umd-lhcb/electronic-projects/backplane/mechanics/19-02-08_stackup_mech_constraints_cern/stackup_28_layers/Stackup_report_for_PathFinder_24_layers.pdf

# STACKUP & IMPEDANCE REPORT

Page 1 of 1

### Planner: SSDC_AMITHR Confidential / Proprietary Information

### Customer Required Finished Thickness: 112.00 (+11.20 / -11.20) mils

### Measured: Over mask on plated copper

### Job Name: Customer:

152496

### Part Name:

### university of maryland Pathfinder

Revision: | A | Estimated Thickness after Lamination: 105.34 mils

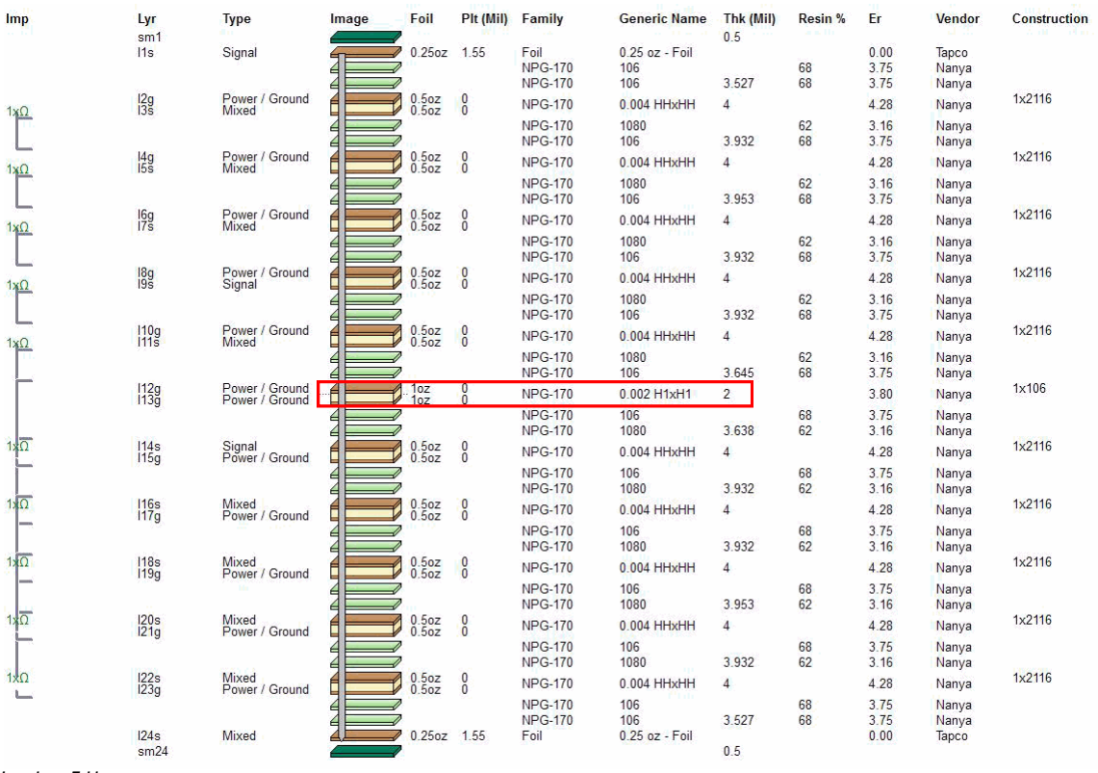
[picture p3: figure]

Index | Layer | Required Impedance [ohms] | Tol [ohms] +/- | Type | Ref 1 | Lower Ref | Orig LW [mil] | Orig Spacing [mil] | Orig CP Spacing [mil] | Finished LW [mil] | Finished Spacing [mil] | Fin. CP Spacing [mil] | Impedance Simulation [ohms] | Impedance before Mask [ohms] | IMG
a | 3 | 100 | 10% | Diff Stripline | 4 | 2 | 3.50 | 4.37 | | 3.00 | 4.87 | | 99.0
b | 5 | 100 | 10% | Diff Stripline | 6 | 4 | 3.50 | 4.37 | | 3.00 | 4.87 | | 99.1
c | 7 | 100 | 10% | Diff Stripline | 8 | 6 | 3.50 | 4.37 | | 3.00 | 4.87 | | 99.0
d | 9 | 100 | 10% | Diff Stripline | 10 | 8 | 3.50 | 4.37 | | 3.00 | 4.87 | | 99.0
e | 11 | 100 | 10% | Diff Stripline | 12 | 10 | 3.50 | 4.37 | | 3.00 | 4.87 | | 97.7
f | 14 | 100 | 10% | Diff Stripline | 13 | 15 | 3.50 | 4.37 | | 3.00 | 4.87 | | 97.7
g | 16 | 100 | 10% | Diff Stripline | 15 | 17 | 3.50 | 4.37 | | 3.00 | 4.87 | | 99.0
h | 18 | 100 | 10% | Diff Stripline | 17 | 19 | 3.50 | 4.37 | | 3.00 | 4.87 | | 99.0
i | 20 | 100 | 10% | Diff Stripline | 19 | 21 | 3.50 | 4.37 | | 3.00 | 4.87 | | 99.1
j | 22 | 100 | 10% | Diff Stripline | 21 | 23 | 3.50 | 4.37 | | 3.00 | 4.87 | | 99.0

Impedance Table

Report Version 1.60 | Report Print Date/Time: 11/16/2018 11:04:43AM | Page 1 of 1
