umd-lhcb/electronic-projects/lvr/UT_LV_DIAGRAMS.pdf

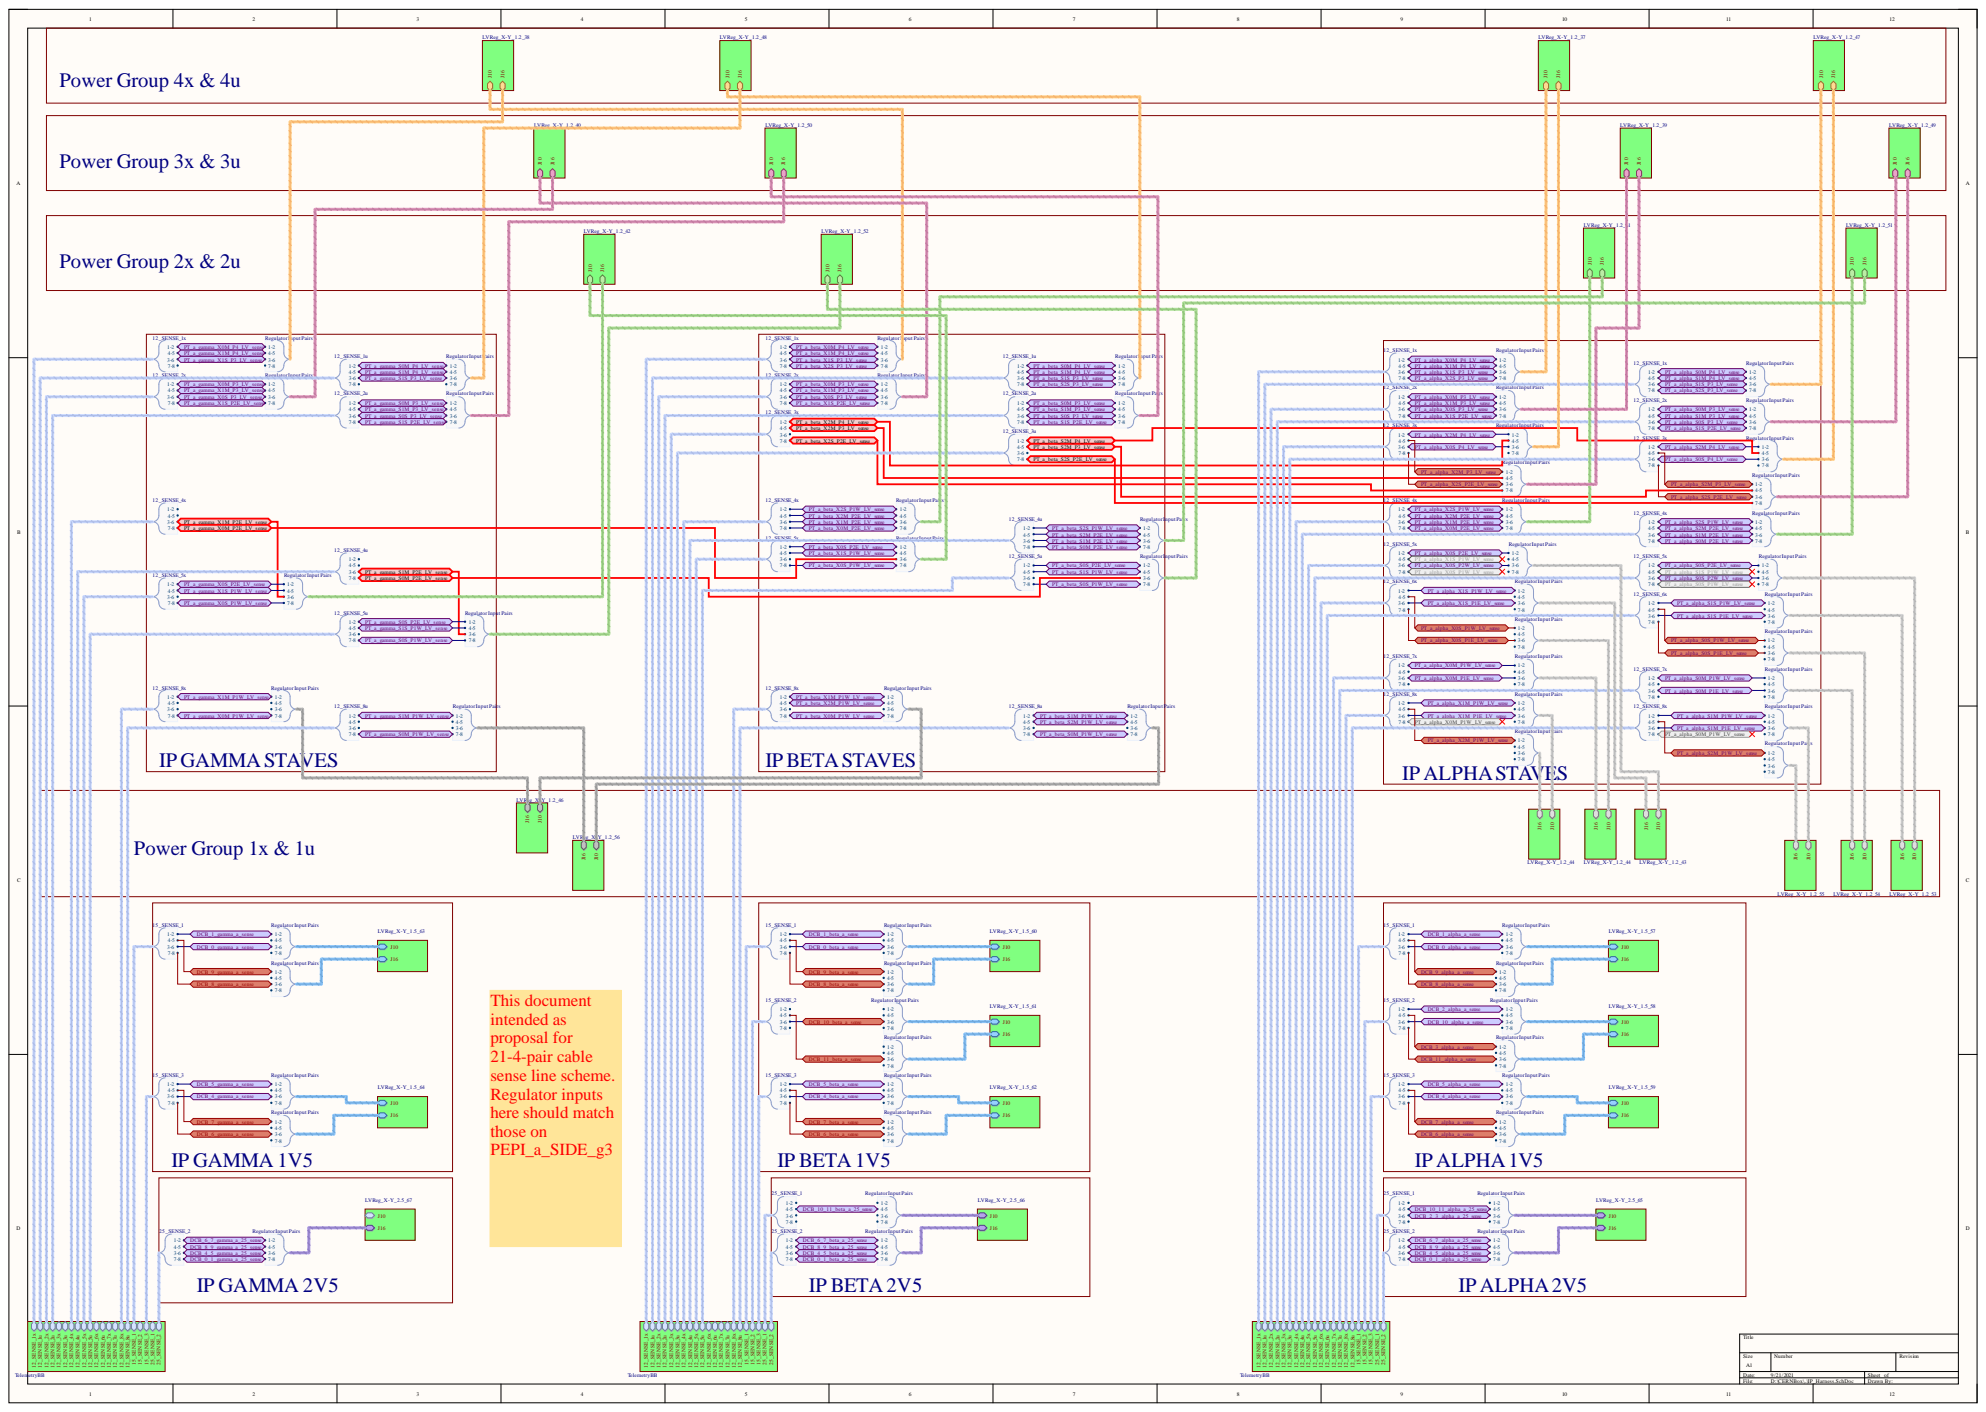
[picture p26: page 1]

12_SENSE_3u | | 1-2 PT_a_alpha_X2M_P4_LV_sense

4-5 PT_a_beta_S2M_P3_LV_sense 3-6 | | 3-6 7-8 | PT_a_alpha_X0S_P4_LV_sense | 1-2 PT_a_alpha_S2M_P4_LV_sense

PT_a_alpha_X2M_P3_LV_sense | Regulator Input Pairs 7-8 1-2 4-5 3-6 7-8 | PT_a_alpha_S2M_P3_LV_sense | 1-2 4-5 3-6 7-8

PT_a_alpha_X2S_P2E_LV_sense

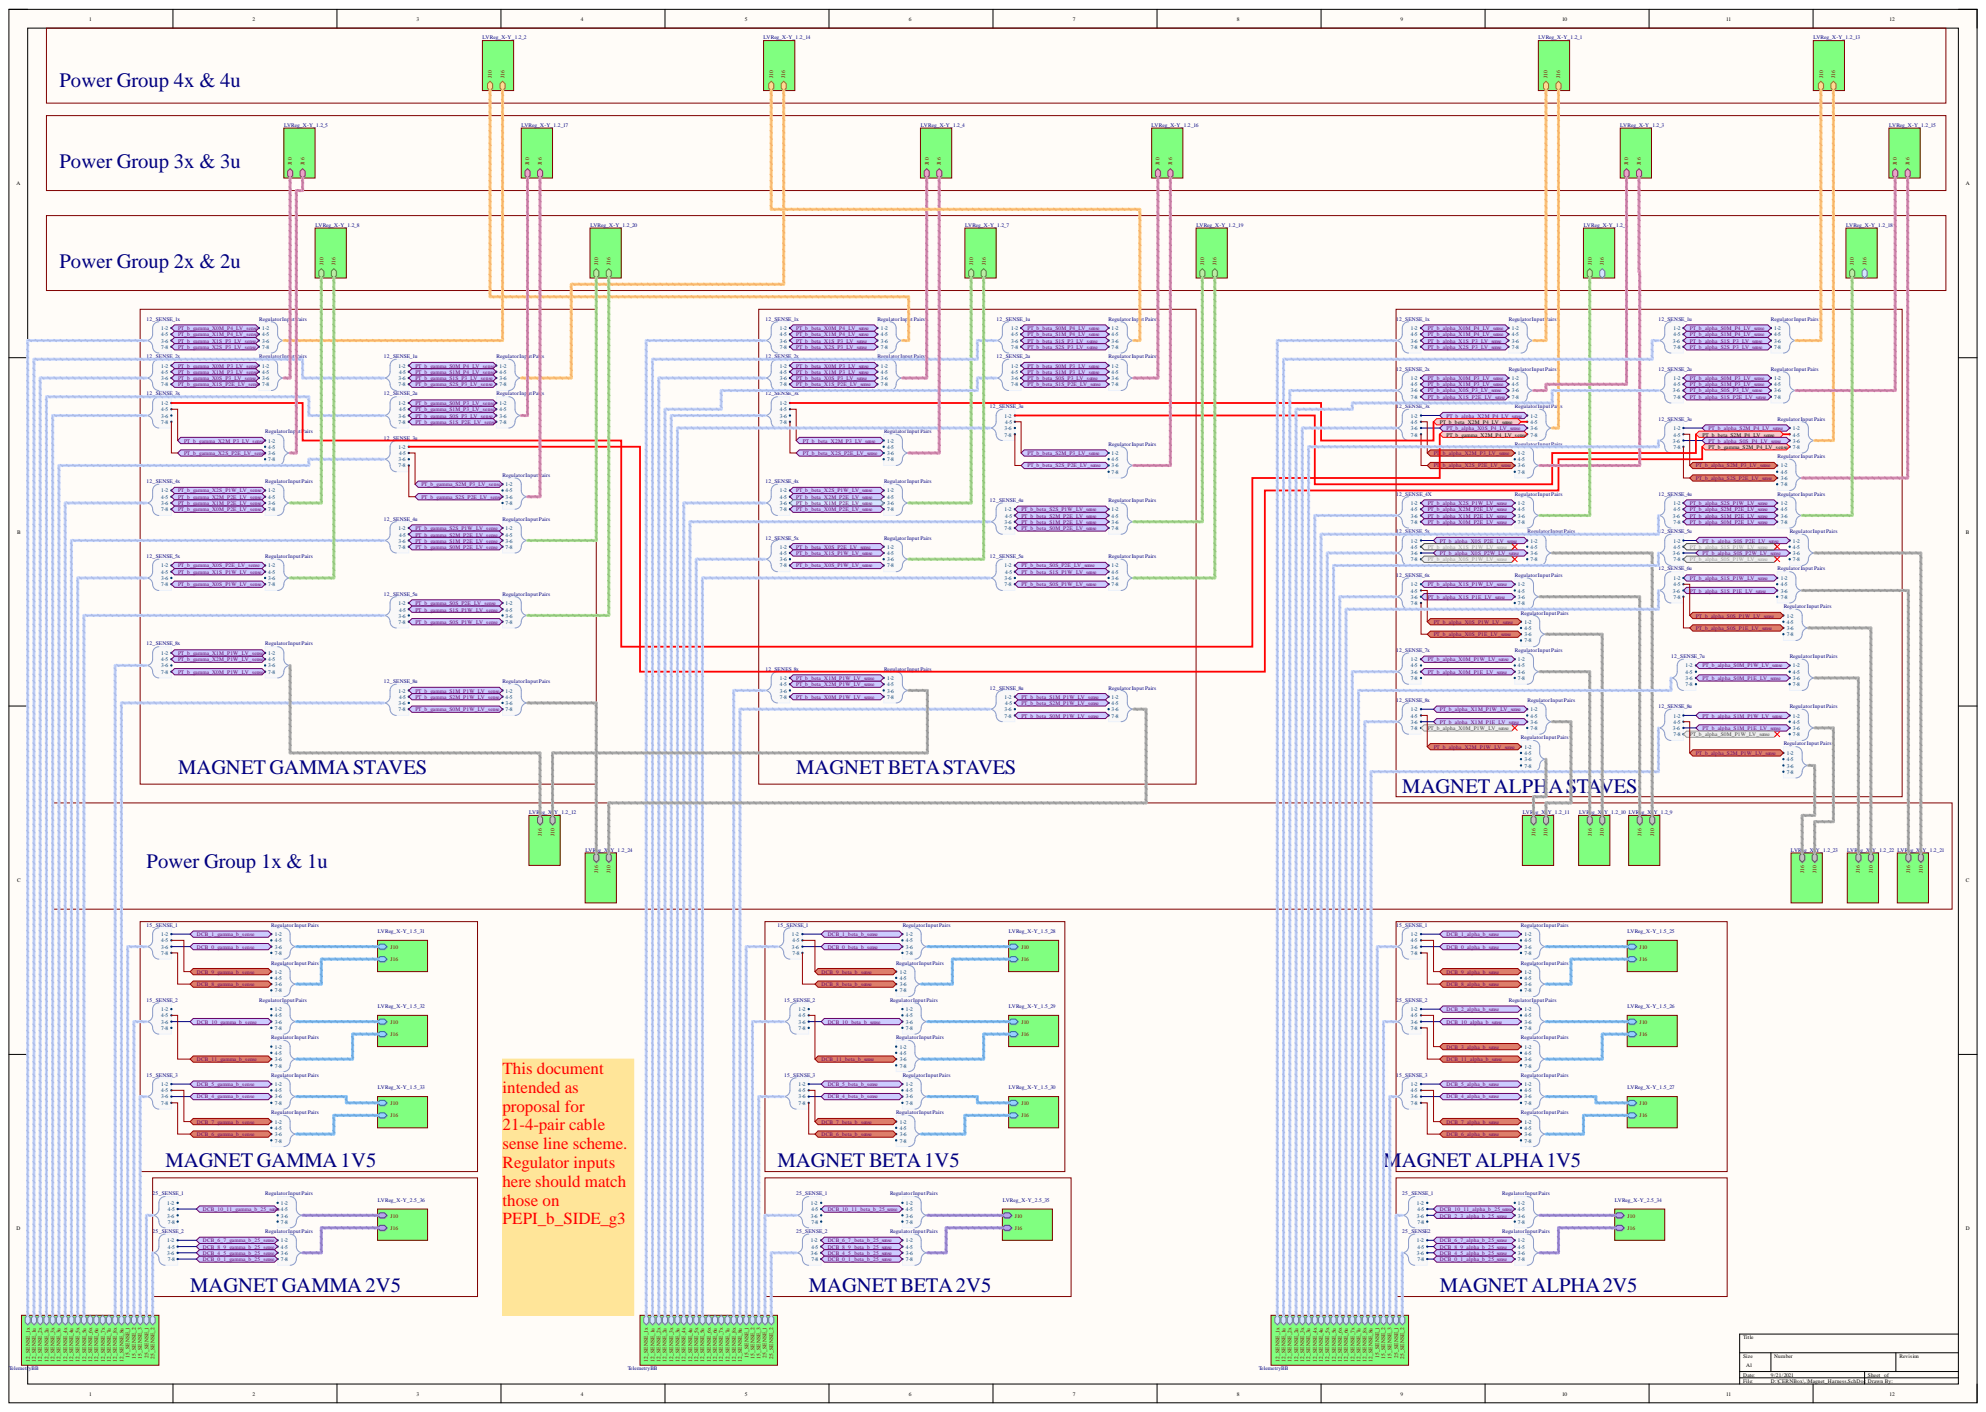
[picture p27: page 2]

7-8 PT_b_gamma_X1S_P2E_LV_sense 7-8 12_SENSE_3x

Regulator Input Pairs | 12_SENSE_3u 1-2 | 12_SENSE_3x 1-2

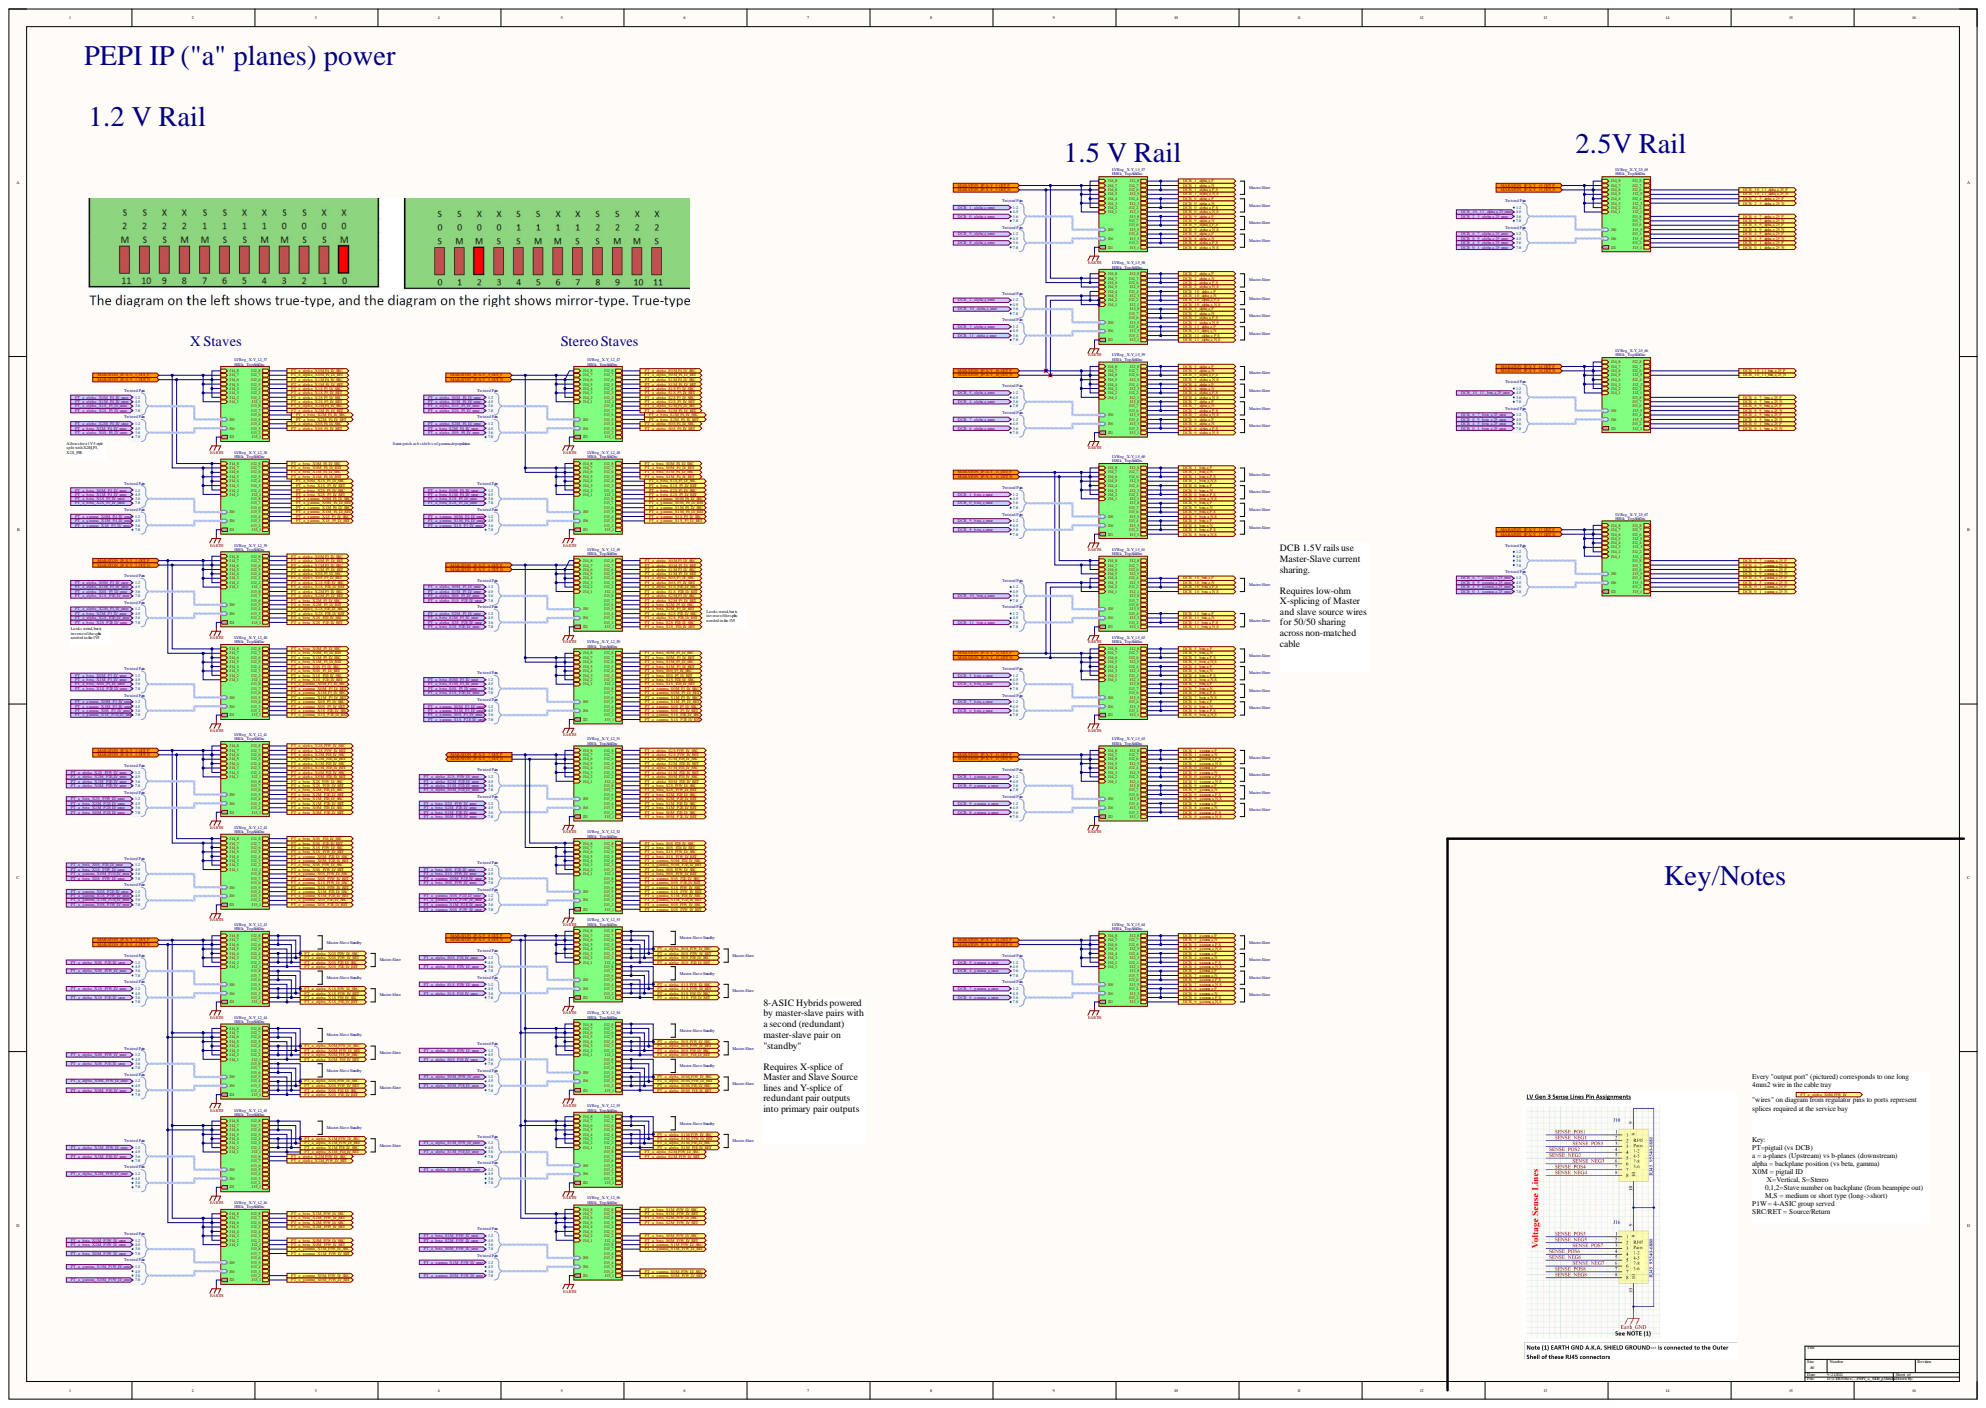
[picture p28: page 3]

PEPI IP ("a" planes) power

Same patch as b side b/c ofgamma depopulation

Requires low-ohm
X-splicing of Master
and slave source wires
for 50/50 sharing
across non-matched
cable

Looks weird, but is
inverse ofthe splits

8-ASIC Hybrids powered
by master-slave pairs with
a second (redundant)
master-slave pair on
"standby"

Requires X-splice of
Master and Slave Source
lines and Y-splice of
redundant pair outputs
into primary pair outputs

Every "output port" (pictured) corresponds to one long
4mm2 wire in the cable tray

"wires" on diagram from regulator pins to ports represent
splices required at the service bay

Key:
PT=pigtail (vs DCB)
a = a-planes (Upstream) vs b-planes (downstream)
alpha = backplane position (vs beta, gamma)
X0M = pigtail ID
X=Vertical, S=Stereo
0,1,2=Stave number on backplane (from beampipe out)
M,S = medium or short type (long->short)
P1W= 4-ASIC group served

SRC/RET = Source/Return

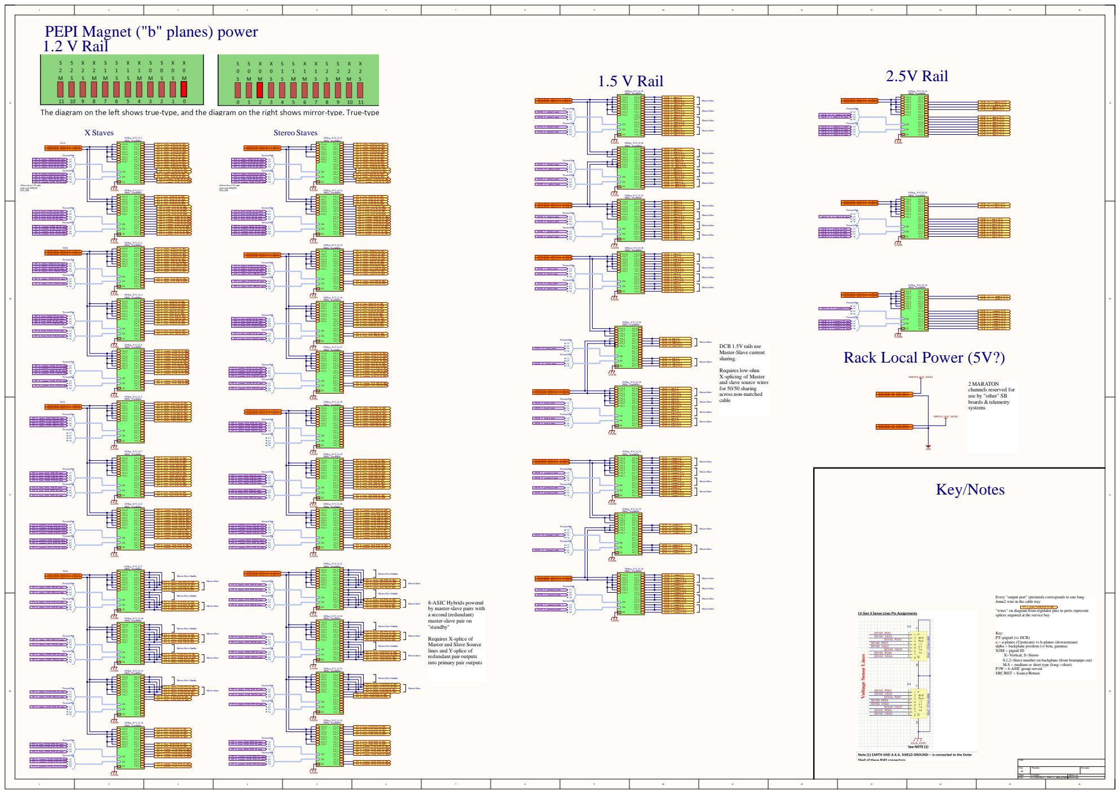
[picture p29: page 4]

PEPI Magnet ("b" planes) power
1.2 V Rail

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

2 MARATON
channels reserved for
use by "other" SB
boards & telemetry
systems

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

Every "output port" (pictured) corresponds to one long
4mm2 wire in the cable tray

"wires" on diagram from regulator pins to ports represent
splices required at the service bay

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

0,1,2=Stave number on backplane (from beampipe out)
M,S = medium or short type (long->short)
P1W= 4-ASIC group served
SRC/RET = Source/Return
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
